mrjoemoe/smart_charger_2point0/smart_charger_pictures/IMG_2177.JPG

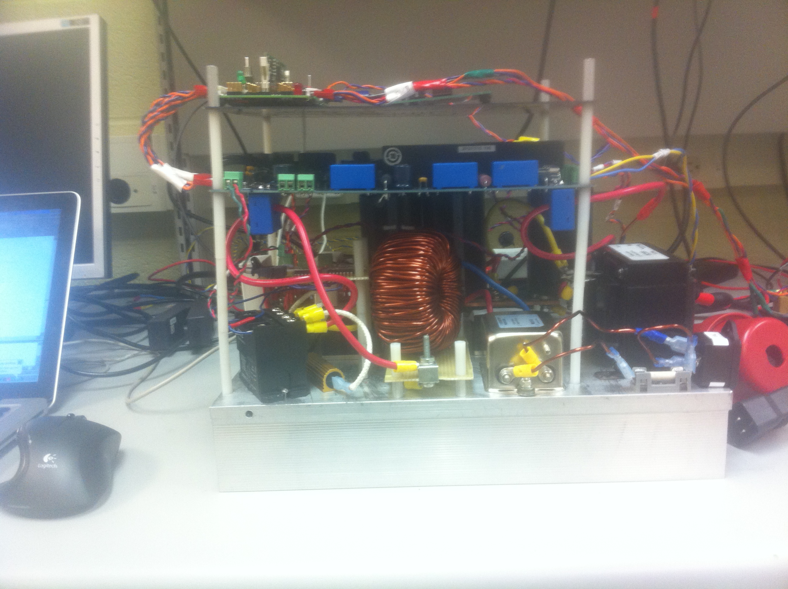
smart_charger_pictures/IMG_2177.JPG
