mrjoemoe/smart_charger_2point0/smart_charger_pictures/IMG_2181.JPG

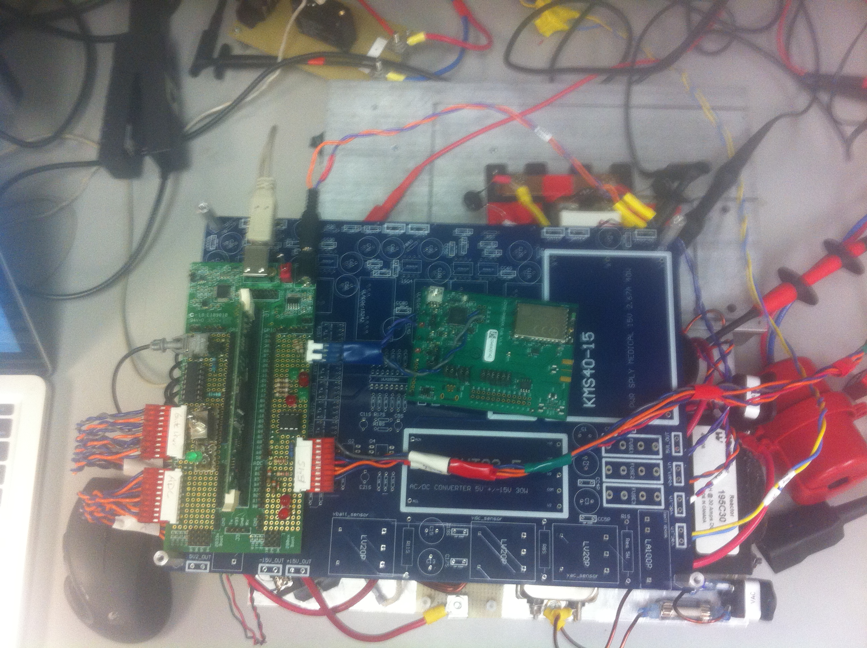
smart_charger_pictures/IMG_2181.JPG
