mrjoemoe/smart_charger_2point0/smart_charger_pictures/IMG_2185.JPG

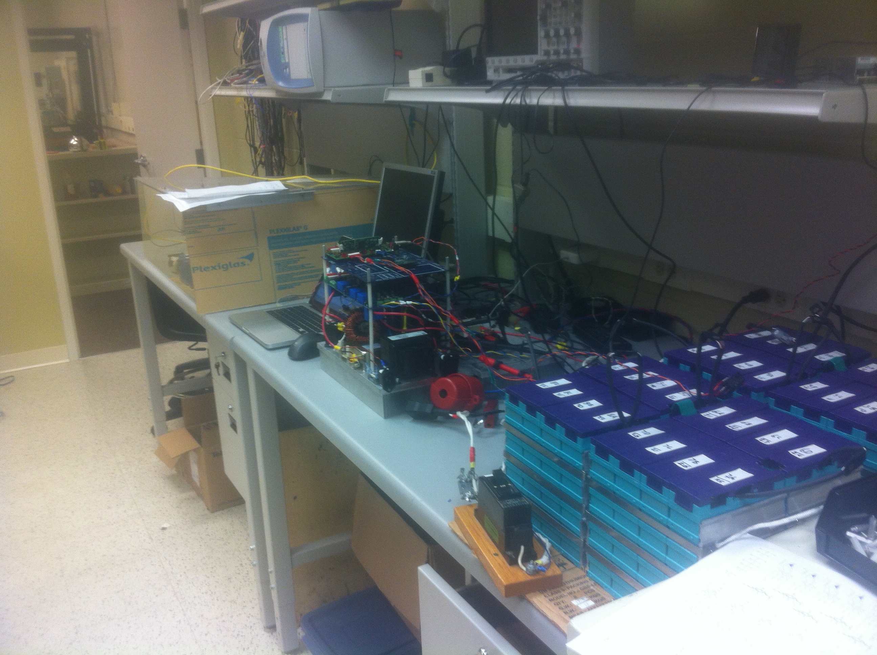
smart_charger_pictures/IMG_2185.JPG
