mrjoemoe/smart_charger_2point0/tms320f2808_firmware/include/IQmathLib.h

// TI File $Revision: /main/3 $
// Checkin $Date: July 8, 2008   16:58:38 $
//###########################################################################
//
// FILE:    IQmathLib.h
//
// TITLE:   IQ Math library functions definitions.
//
//###########################################################################
//
// Ver  | dd-mmm-yyyy |  Who  | Description of changes
// =====|=============|=======|==============================================
//  1.3 | 19 Nov 2001 | A. T. | Original Release.
// -----|-------------|-------|----------------------------------------------
//  1.4 | 17 May 2002 | A. T. | Added new functions and support for
//      |             |       | intrinsics IQmpy, IQxmpy, IQsat.
// -----|-------------|-------|----------------------------------------------
//  1.4a| 12 Jun 2002 | A. T. | Fixed problem with _IQ() operation on
//      |             |       | variables.
// -----|-------------|-------|----------------------------------------------
//  1.4b| 18 Jun 2002 | A. T. | Fixed bug with _IQtoIQN() and _IQNtoIQ()
//      |             |       | operations.
// -----|-------------|-------|----------------------------------------------
//  1.4d| 30 Mar 2003 | DA/SD | 1. Added macro parameters in parentheses
//      |             |       |    in number of places where it matters
//      |             |       | 2. Added macro definition to include header
//      |             |       |    file multiple times in the program.
// -----|-------------|-------|----------------------------------------------
//  1.4e| 17 Jun 2004 | AT/DA | Added IQexp function.
//      |             |       | Added IQasin & IQacos functions (thanks DA).
// -----|-------------|-------|----------------------------------------------
//  1.4f| 10 Mar 2005 | AT    | Fixed Bug In IQexp function.
// -----|-------------|-------|----------------------------------------------
//  1.5 | 30 Jan 2008 | LH    | 1. Changed the definion of the _IQatan2PU(A,B)
//      |             |       |    macro for FLOAT_MATH so that a call to
//      |             |       |    divide will not occur.
//      |             |       | 2. If MATH_TYPE == FLOAT_MATH, then include the
//      |             |       |    following standard headers: math.h
//      |             |       |    stdlib.h.
//      |             |       | 3. Added missing #defines for the non-global
//      |             |       |    _IQatanN() function
//      |             |       | 4. Adding missing definitions for absolute
//      |             |       |    value when MATH_TYPE == FLOAT_MATH
//      |             |       | 5. Included limits.h and changed the definition
//      |             |       |    of MAX_IQ_NEG to LONG_MIN and MAX_IQ_POS
//      |             |       |    to LONG_MAX
//###########################################################################
// $TI Release: IQmath V1.5a $
// $Release Date: June 2, 2009 $
//###########################################################################
//
// User needs to configure "MATH_TYPE" and "GLOBAL_Q" values:
//
//---------------------------------------------------------------------------
// Select math type, IQ_MATH or FLOAT_MATH:
//

#ifndef __IQMATHLIB_H_INCLUDED__
#define __IQMATHLIB_H_INCLUDED__


#define   FLOAT_MATH     1
#define   IQ_MATH        0

#ifndef   MATH_TYPE
#define   MATH_TYPE      IQ_MATH
#endif

//---------------------------------------------------------------------------
// Select global Q value and scaling. The Q value is limited to the
// following range for all functions:
//
//        30 <= GLOBAL_Q <=  1
//
#ifndef   GLOBAL_Q
#define   GLOBAL_Q       19
#endif

//---------------------------------------------------------------------------
// If using FLOAT_MATH, include standard headers to avoid conversion issues
//
#if MATH_TYPE == FLOAT_MATH
#include <math.h>
#include <stdlib.h>
#endif
#include <limits.h>

//---------------------------------------------------------------------------
// Various Usefull Constant Definitions:
//
#define   QG          GLOBAL_Q
#define   Q30         30
#define   Q29         29
#define   Q28         28
#define   Q27         27
#define   Q26         26
#define   Q25         25
#define   Q24         24
#define   Q23         23
#define   Q22         22
#define   Q21         21
#define   Q20         20
#define   Q19         19
#define   Q18         18
#define   Q17         17
#define   Q16         16
#define   Q15         15
#define   Q14         14
#define   Q13         13
#define   Q12         12
#define   Q11         11
#define   Q10         10
#define   Q9          9
#define   Q8          8
#define   Q7          7
#define   Q6          6
#define   Q5          5
#define   Q4          4
#define   Q3          3
#define   Q2          2
#define   Q1          1

#define   MAX_IQ_POS  LONG_MAX
#define   MAX_IQ_NEG  LONG_MIN
#define   MIN_IQ_POS  1
#define   MIN_IQ_NEG  -1

//###########################################################################
#if MATH_TYPE == IQ_MATH
//###########################################################################
// If IQ_MATH is used, the following IQmath library function definitions
// are used:
//===========================================================================
typedef   long    _iq;
typedef   long    _iq30;
typedef   long    _iq29;
typedef   long    _iq28;
typedef   long    _iq27;
typedef   long    _iq26;
typedef   long    _iq25;
typedef   long    _iq24;
typedef   long    _iq23;
typedef   long    _iq22;
typedef   long    _iq21;
typedef   long    _iq20;
typedef   long    _iq19;
typedef   long    _iq18;
typedef   long    _iq17;
typedef   long    _iq16;
typedef   long    _iq15;
typedef   long    _iq14;
typedef   long    _iq13;
typedef   long    _iq12;
typedef   long    _iq11;
typedef   long    _iq10;
typedef   long    _iq9;
typedef   long    _iq8;
typedef   long    _iq7;
typedef   long    _iq6;
typedef   long    _iq5;
typedef   long    _iq4;
typedef   long    _iq3;
typedef   long    _iq2;
typedef   long    _iq1;
//---------------------------------------------------------------------------
#define   _IQ30(A)      (long) ((A) * 1073741824.0L)
#define   _IQ29(A)      (long) ((A) * 536870912.0L)
#define   _IQ28(A)      (long) ((A) * 268435456.0L)
#define   _IQ27(A)      (long) ((A) * 134217728.0L)
#define   _IQ26(A)      (long) ((A) * 67108864.0L)
#define   _IQ25(A)      (long) ((A) * 33554432.0L)
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
extern    int  _IQ5toa(char *A, const char *B, long C);
extern    int  _IQ4toa(char *A, const char *B, long C);
extern    int  _IQ3toa(char *A, const char *B, long C);
extern    int  _IQ2toa(char *A, const char *B, long C);
extern    int  _IQ1toa(char *A, const char *B, long C);


#define   _IQ30toa(A, B, C)   __IQNtoa(A, B, C, 30);
#define   _IQ29toa(A, B, C)   __IQNtoa(A, B, C, 29);
#define   _IQ28toa(A, B, C)   __IQNtoa(A, B, C, 28);
#define   _IQ27toa(A, B, C)   __IQNtoa(A, B, C, 27);
#define   _IQ26toa(A, B, C)   __IQNtoa(A, B, C, 26);
#define   _IQ25toa(A, B, C)   __IQNtoa(A, B, C, 25);
#define   _IQ24toa(A, B, C)   __IQNtoa(A, B, C, 24);
#define   _IQ23toa(A, B, C)   __IQNtoa(A, B, C, 23);
#define   _IQ21toa(A, B, C)   __IQNtoa(A, B, C, 21);
#define   _IQ22toa(A, B, C)   __IQNtoa(A, B, C, 22);
#define   _IQ20toa(A, B, C)   __IQNtoa(A, B, C, 20);
#define   _IQ19toa(A, B, C)   __IQNtoa(A, B, C, 19);
#define   _IQ18toa(A, B, C)   __IQNtoa(A, B, C, 18);
#define   _IQ17toa(A, B, C)   __IQNtoa(A, B, C, 17);
#define   _IQ16toa(A, B, C)   __IQNtoa(A, B, C, 16);
#define   _IQ15toa(A, B, C)   __IQNtoa(A, B, C, 15);
#define   _IQ14toa(A, B, C)   __IQNtoa(A, B, C, 14);
#define   _IQ13toa(A, B, C)   __IQNtoa(A, B, C, 13);
#define   _IQ12toa(A, B, C)   __IQNtoa(A, B, C, 12);
#define   _IQ11toa(A, B, C)   __IQNtoa(A, B, C, 11);
#define   _IQ10toa(A, B, C)   __IQNtoa(A, B, C, 10);
#define   _IQ9toa(A, B, C)    __IQNtoa(A, B, C, 9);
#define   _IQ8toa(A, B, C)    __IQNtoa(A, B, C, 8);
#define   _IQ7toa(A, B, C)    __IQNtoa(A, B, C, 7);
#define   _IQ6toa(A, B, C)    __IQNtoa(A, B, C, 6);
#define   _IQ5toa(A, B, C)    __IQNtoa(A, B, C, 5);
#define   _IQ4toa(A, B, C)    __IQNtoa(A, B, C, 4);
#define   _IQ3toa(A, B, C)    __IQNtoa(A, B, C, 3);
#define   _IQ2toa(A, B, C)    __IQNtoa(A, B, C, 2);
#define   _IQ1toa(A, B, C)    __IQNtoa(A, B, C, 1);


#if GLOBAL_Q == 30
#define   _IQtoa(A, B, C)     __IQNtoa(A, B, C, 30)
#endif
#if GLOBAL_Q == 29
#define   _IQtoa(A, B, C)     __IQNtoa(A, B, C, 29)
#endif
#if GLOBAL_Q == 28
#define   _IQtoa(A, B, C)     __IQNtoa(A, B, C, 28)
#endif
#if GLOBAL_Q == 27
#define   _IQtoa(A, B, C)     __IQNtoa(A, B, C, 27)
#endif
#if GLOBAL_Q == 26
#define   _IQtoa(A, B, C)     __IQNtoa(A, B, C, 26)
#endif
#if GLOBAL_Q == 25
#define   _IQtoa(A, B, C)     __IQNtoa(A, B, C, 25)
#endif
#if GLOBAL_Q == 24
#define   _IQtoa(A, B, C)     __IQNtoa(A, B, C, 24)
#endif
#if GLOBAL_Q == 23
#define   _IQtoa(A, B, C)     __IQNtoa(A, B, C, 23)
#endif
#if GLOBAL_Q == 22
#define   _IQtoa(A, B, C)     __IQNtoa(A, B, C, 22)
#endif
#if GLOBAL_Q == 21
#define   _IQtoa(A, B, C)     __IQNtoa(A, B, C, 21)
#endif
#if GLOBAL_Q == 20
#define   _IQtoa(A, B, C)     __IQNtoa(A, B, C, 20)
#endif
#if GLOBAL_Q == 19
#define   _IQtoa(A, B, C)     __IQNtoa(A, B, C, 19)
#endif
#if GLOBAL_Q == 18
#define   _IQtoa(A, B, C)     __IQNtoa(A, B, C, 18)
#endif
#if GLOBAL_Q == 17
#define   _IQtoa(A, B, C)     __IQNtoa(A, B, C, 17)
#endif
#if GLOBAL_Q == 16
#define   _IQtoa(A, B, C)     __IQNtoa(A, B, C, 16)
#endif
#if GLOBAL_Q == 15
#define   _IQtoa(A, B, C)     __IQNtoa(A, B, C, 15)
#endif
#if GLOBAL_Q == 14
#define   _IQtoa(A, B, C)     __IQNtoa(A, B, C, 14)
#endif
#if GLOBAL_Q == 13
#define   _IQtoa(A, B, C)     __IQNtoa(A, B, C, 13)
#endif
#if GLOBAL_Q == 12
#define   _IQtoa(A, B, C)     __IQNtoa(A, B, C, 12)
#endif
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
#define   _IQtoQ14(A)    (short) ((long)((A) * 16384.0L))
#define   _IQtoQ13(A)    (short) ((long)((A) * 8192.0L))
#define   _IQtoQ12(A)    (short) ((long)((A) * 4096.0L))
#define   _IQtoQ11(A)    (short) ((long)((A) * 2048.0L))
#define   _IQtoQ10(A)    (short) ((long)((A) * 1024.0L))
#define   _IQtoQ9(A)     (short) ((long)((A) * 512.0L))
#define   _IQtoQ8(A)     (short) ((long)((A) * 256.0L))
#define   _IQtoQ7(A)     (short) ((long)((A) * 128.0L))
#define   _IQtoQ6(A)     (short) ((long)((A) * 64.0L))
#define   _IQtoQ5(A)     (short) ((long)((A) * 32.0L))
#define   _IQtoQ4(A)     (short) ((long)((A) * 16.0L))
#define   _IQtoQ3(A)     (short) ((long)((A) * 8.0L))
#define   _IQtoQ2(A)     (short) ((long)((A) * 4.0L))
#define   _IQtoQ1(A)     (short) ((long)((A) * 2.0L))
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
